Rocketdude1984/AeroWeather/Parts/Main/Prints/EchoWeather_StevensonScreen_parts/AKMAX_EchoWeather_StevensonScreen.3mf

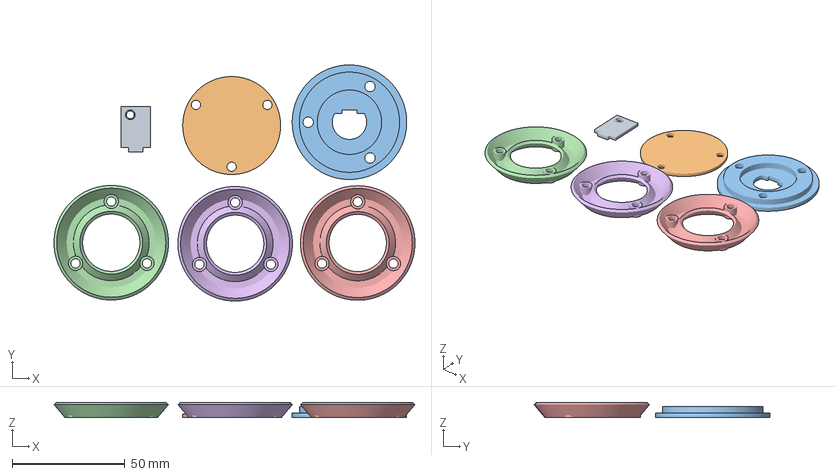
[picture p15: CAD file, 2025-07-23]
Parts/Main/Prints/EchoWeather_StevensonScreen_parts/AKMAX_EchoWeather_StevensonScreen.3mf
160.1 x 104.7 x 6.86 mm
EchoWeather_StevensonScreen_Holder.stl
EchoWeather_StevensonScreen_Bottom.stl
EchoWeather_StevensonScreen_Adapter.stl
EchoWeather_StevensonScreen_Ring.stl(1)
EchoWeather_StevensonScreen_Ring.stl(2)
EchoWeather_StevensonScreen_Ring.stl(3)
