Rocketdude1984/AeroWeather/Parts/Windvane/WindVane_Print/Aeroweather_Windvane_VaneHolder.stl

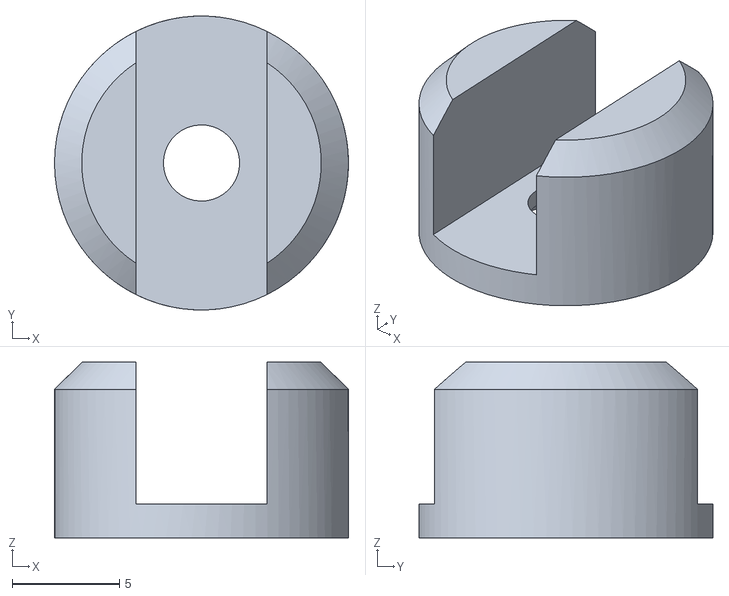
[picture p16: CAD file, 2025-07-23]
Parts/Windvane/WindVane_Print/Aeroweather_Windvane_VaneHolder.stl
13.7 x 13.7 x 8.19
