Rocketdude1984/AeroWeather/Parts/Main/Prints/EchoWeather_StevensonScreen_parts/EchoWeather_StevensonScreen_PREVIEW.stl

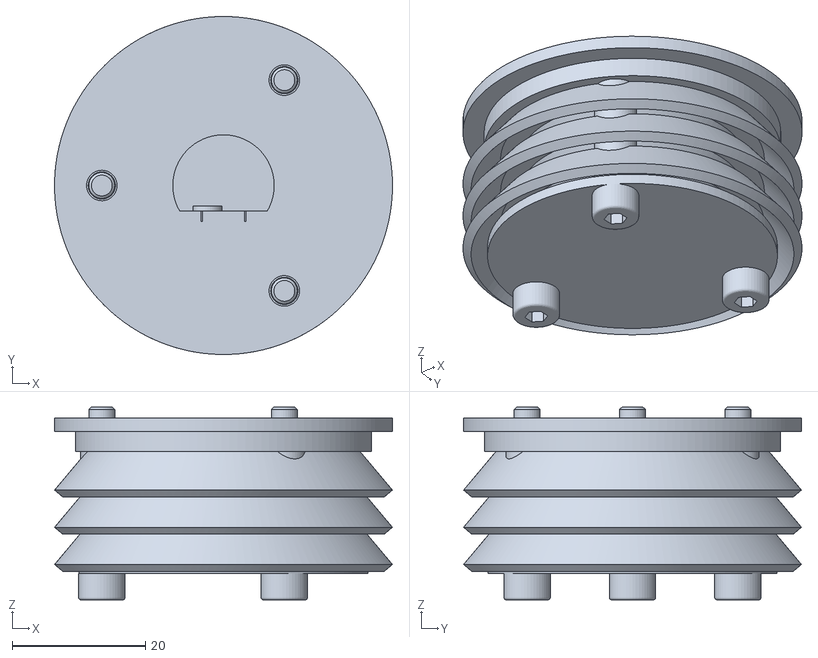
[picture p17: CAD file, 2025-07-16]
Parts/Main/Prints/EchoWeather_StevensonScreen_parts/EchoWeather_StevensonScreen_PREVIEW.stl
50.8 x 50.8 x 29.0
