Rocketdude1984/AeroWeather/Parts/Windvane/WindVane_Print/Aeroweather_Windvane_Enclosure.stl

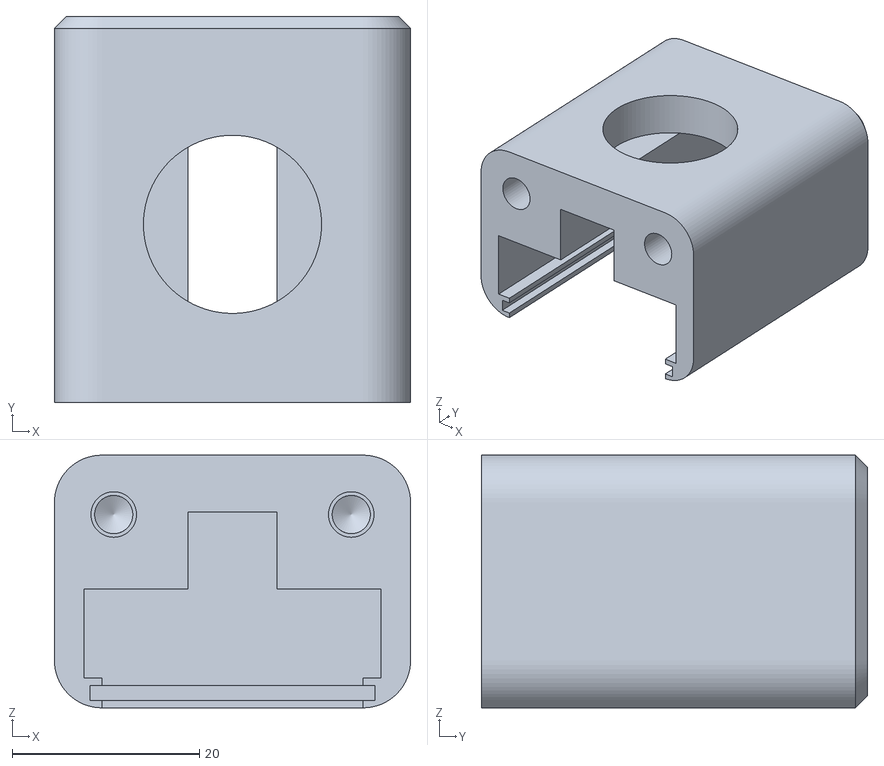
[picture p18: CAD file, 2025-07-23]
Parts/Windvane/WindVane_Print/Aeroweather_Windvane_Enclosure.stl
38.1 x 41.3 x 27.0
