Rocketdude1984/AeroWeather/Parts/Windvane/WindVane_Print/Aeroweather_Windvane_Lid.stl

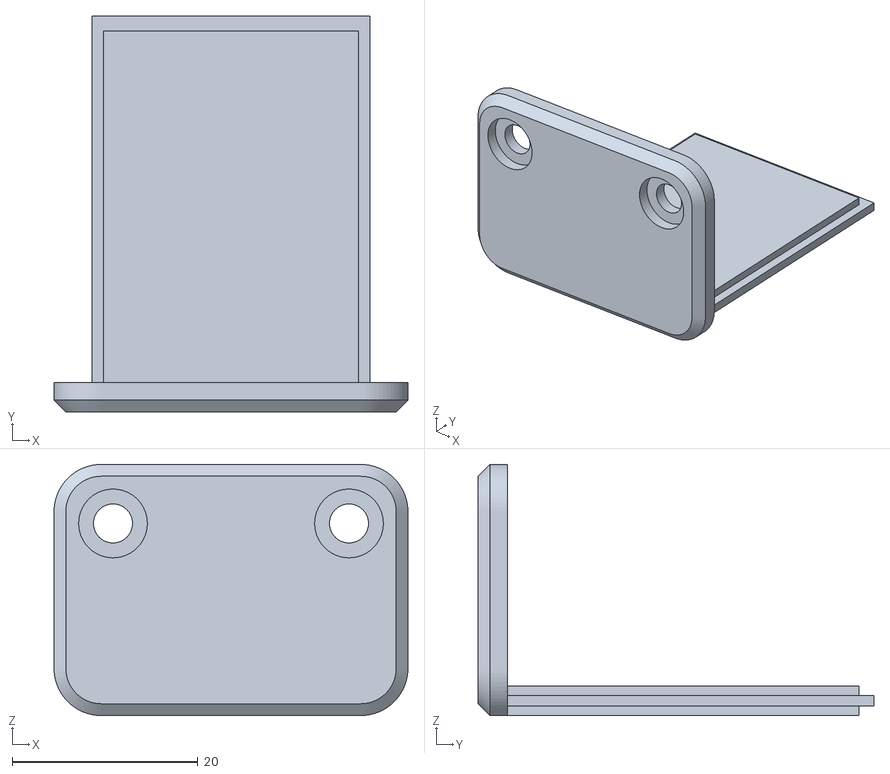
[picture p19: CAD file, 2025-07-23]
Parts/Windvane/WindVane_Print/Aeroweather_Windvane_Lid.stl
38.1 x 42.6 x 27.0
